jakopako/lumaire/arduino/lumaire/BlowClassifier.h

// Label mapping{'blow' : 0, 'nope' : 1, 'suck' : 2}
// score 0.9775725593667546
//         [0.96710526 0.98019802 0.97689769 0.97029703 0.97689769]
//         precision recall f1 - score support

//     0 0.95 0.96 0.95 273
//     1 0.98 0.99 0.99 1216
//     2 0.95 0.70 0.81 27

//     accuracy 0.98 1516
//     macro avg 0.96 0.88 0.92 1516
//     weighted avg 0.98 0.98 0.98 1516

#ifndef UUID1727902892720
#define UUID1727902892720

/**
 * BlowRandomForestClassifier(bootstrap=True, ccp_alpha=0.0, class_name=RandomForestClassifier, class_weight=None, criterion=gini, estimator=DecisionTreeClassifier(), estimator_params=('criterion', 'max_depth', 'min_samples_split', 'min_samples_leaf', 'min_weight_fraction_leaf', 'max_features', 'max_leaf_nodes', 'min_impurity_decrease', 'random_state', 'ccp_alpha', 'monotonic_cst'), max_depth=None, max_features=sqrt, max_leaf_nodes=None, max_samples=None, min_impurity_decrease=0.0, min_samples_leaf=1, min_samples_split=2, min_weight_fraction_leaf=0.0, monotonic_cst=None, n_estimators=10, n_jobs=None, num_outputs=3, oob_score=False, package_name=everywhereml.sklearn.ensemble, random_state=None, template_folder=everywhereml/sklearn/ensemble, verbose=0, warm_start=False)
 */
class BlowRandomForestClassifier
{
public:
    /**
     * Predict class from features
     */
    int predict(float *x)
    {
        int predictedValue = 0;
        size_t startedAt = micros();

        float votes[3] = {0};
        uint8_t classIdx = 0;
        float classScore = 0;

        tree0(x, &classIdx, &classScore);
        votes[classIdx] += classScore;

        tree1(x, &classIdx, &classScore);
        votes[classIdx] += classScore;

        tree2(x, &classIdx, &classScore);
        votes[classIdx] += classScore;

        tree3(x, &classIdx, &classScore);
        votes[classIdx] += classScore;

        tree4(x, &classIdx, &classScore);
        votes[classIdx] += classScore;

        tree5(x, &classIdx, &classScore);
        votes[classIdx] += classScore;

        tree6(x, &classIdx, &classScore);
        votes[classIdx] += classScore;

        tree7(x, &classIdx, &classScore);
        votes[classIdx] += classScore;

        tree8(x, &classIdx, &classScore);
        votes[classIdx] += classScore;

        tree9(x, &classIdx, &classScore);
        votes[classIdx] += classScore;

        uint8_t maxClassIdx = 0;
        float maxVote = votes[0];

        for (uint8_t i = 1; i < 3; i++)
        {
            if (votes[i] > maxVote)
            {
                maxClassIdx = i;
                maxVote = votes[i];
            }
        }

        predictedValue = maxClassIdx;

        latency = micros() - startedAt;

        return (lastPrediction = predictedValue);
    }

    /**
     * Get latency in micros
     */
    uint32_t latencyInMicros()
    {
        return latency;
    }

    /**
     * Get latency in millis
     */
    uint16_t latencyInMillis()
    {
        return latency / 1000;
    }

protected:
    float latency = 0;
    int lastPrediction = 0;

    /**
     * Random forest's tree #0
     */
    void tree0(float *x, uint8_t *classIdx, float *classScore)
    {

        if (x[3] < 6143.695068359375)
        {

            if (x[1] < 31.46500015258789)
            {

                if (x[0] < 300.0849914550781)
                {

                    if (x[0] < 69.52999877929688)
                    {

                        if (x[3] < 864.239990234375)
                        {

                            if (x[0] < 25.380000114440918)
                            {

                                if (x[3] < 117.22000122070312)
                                {

                                    *classIdx = 1;
                                    *classScore = 0.7806578087562622;
                                    return;
                                }
                                else
                                {

                                    if (x[3] < 117.33000183105469)
                                    {

                                        *classIdx = 2;
                                        *classScore = 0.017861032454802875;
                                        return;
                                    }
                                    else
                                    {

                                        *classIdx = 1;
                                        *classScore = 0.7806578087562622;
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

                                *classIdx = 2;
                                *classScore = 0.0163363101720758;
                                return;
                            }
                        }
                    }
                    else
                    {
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
